iank/julia_lcd/src/fpga/img/js_sim.png

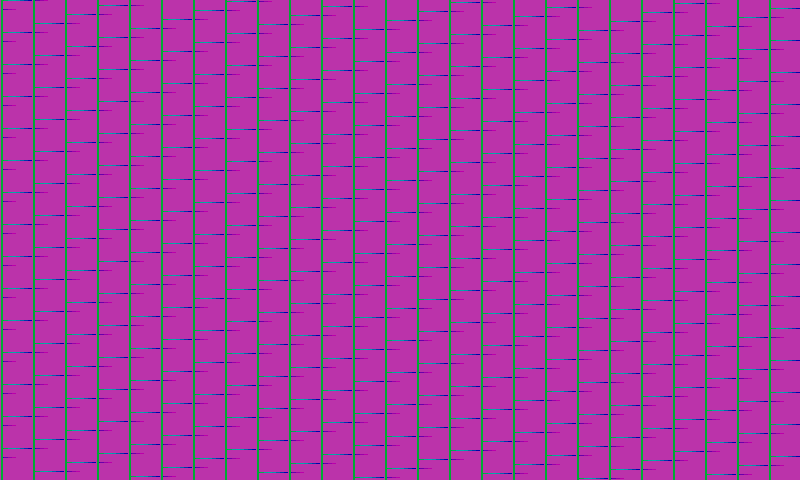
src/fpga/img/js_sim.png
