iank/julia_lcd/src/fpga/gen_colormap.py

#!/usr/bin/env python3
import colorsys

header = '''
module color_map
(
    input [7:0] value,
    output reg [23:0] rgb
);
    always @(*) begin
        case (value)
'''

footer = '''
        endcase
    end
endmodule
'''

print(header)

for i in range(128):
    hue = i / 128;
    sat = 0.6
    val = 1

    rgb = colorsys.hsv_to_rgb(hue, sat, val)
    rgb_hex = ''.join(['%02x' % round(x*255) for x in rgb])
    rgb_mix = ''.join(['%02x' % round(max(x*255 - 50, 0)) for x in rgb])

    print(' '*12, "8'd{0: <3} : rgb = 24'h{1};".format(i, rgb_hex))
    print(' '*12, "8'd{0: <3} : rgb = 24'h{1};".format(i+128, rgb_mix))

print(footer)
